sarinkhan/Rlieh/fritzing/base_circuit02.jpg

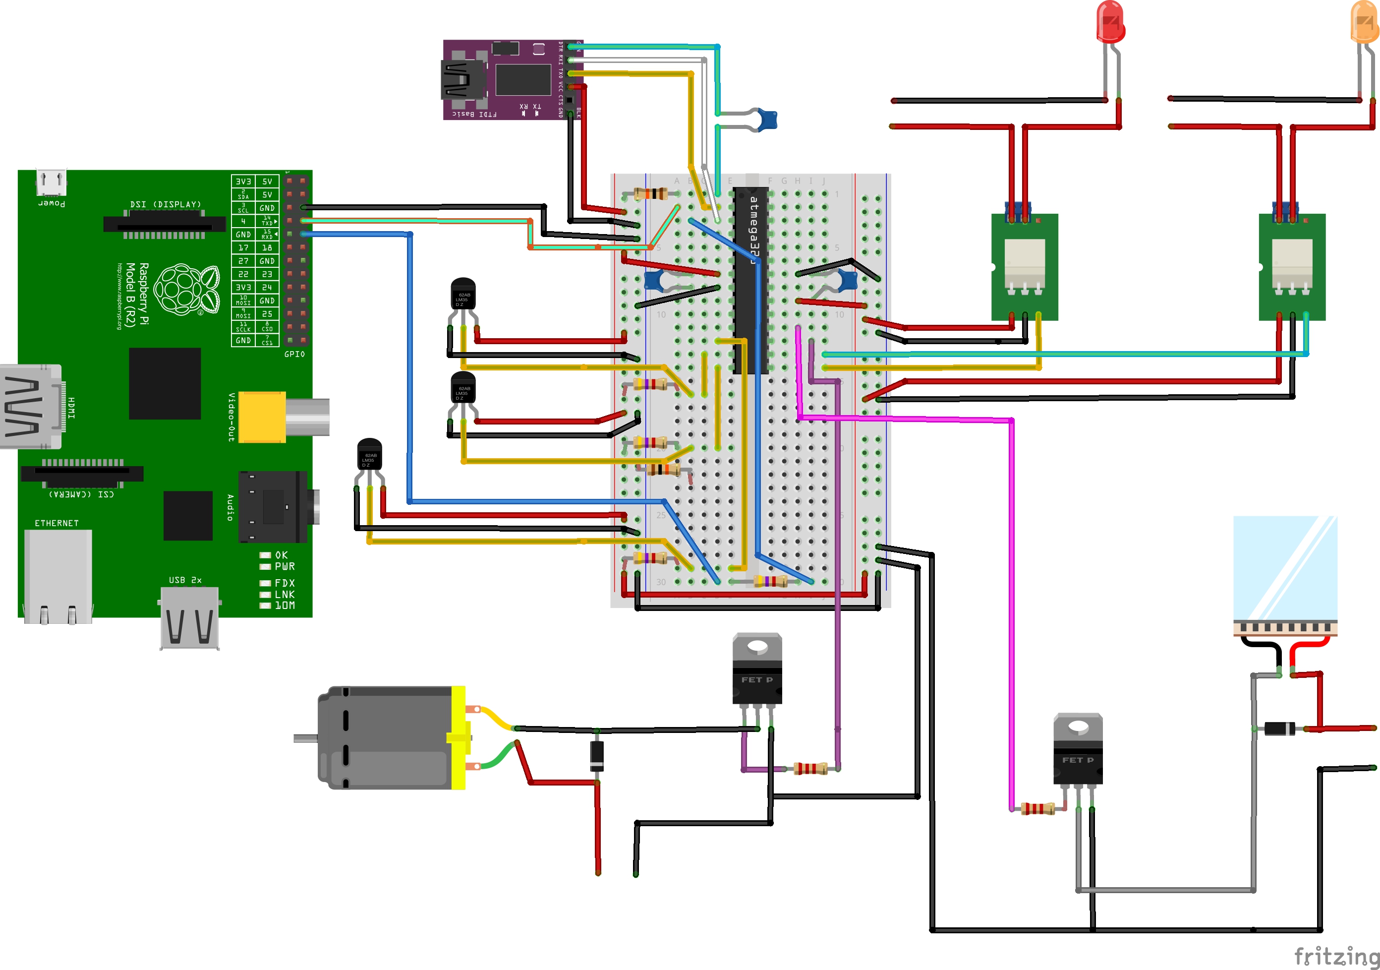
fritzing/base_circuit02.jpg
